goriponsoft/16bitBank-MEGAROM-Controller-74670/16bitBank-MEGAROM-Controller_74670.kicad_sch

## KiCad design 16bitBank-MEGAROM-Controller_74670.kicad_sch (2024-03-24)

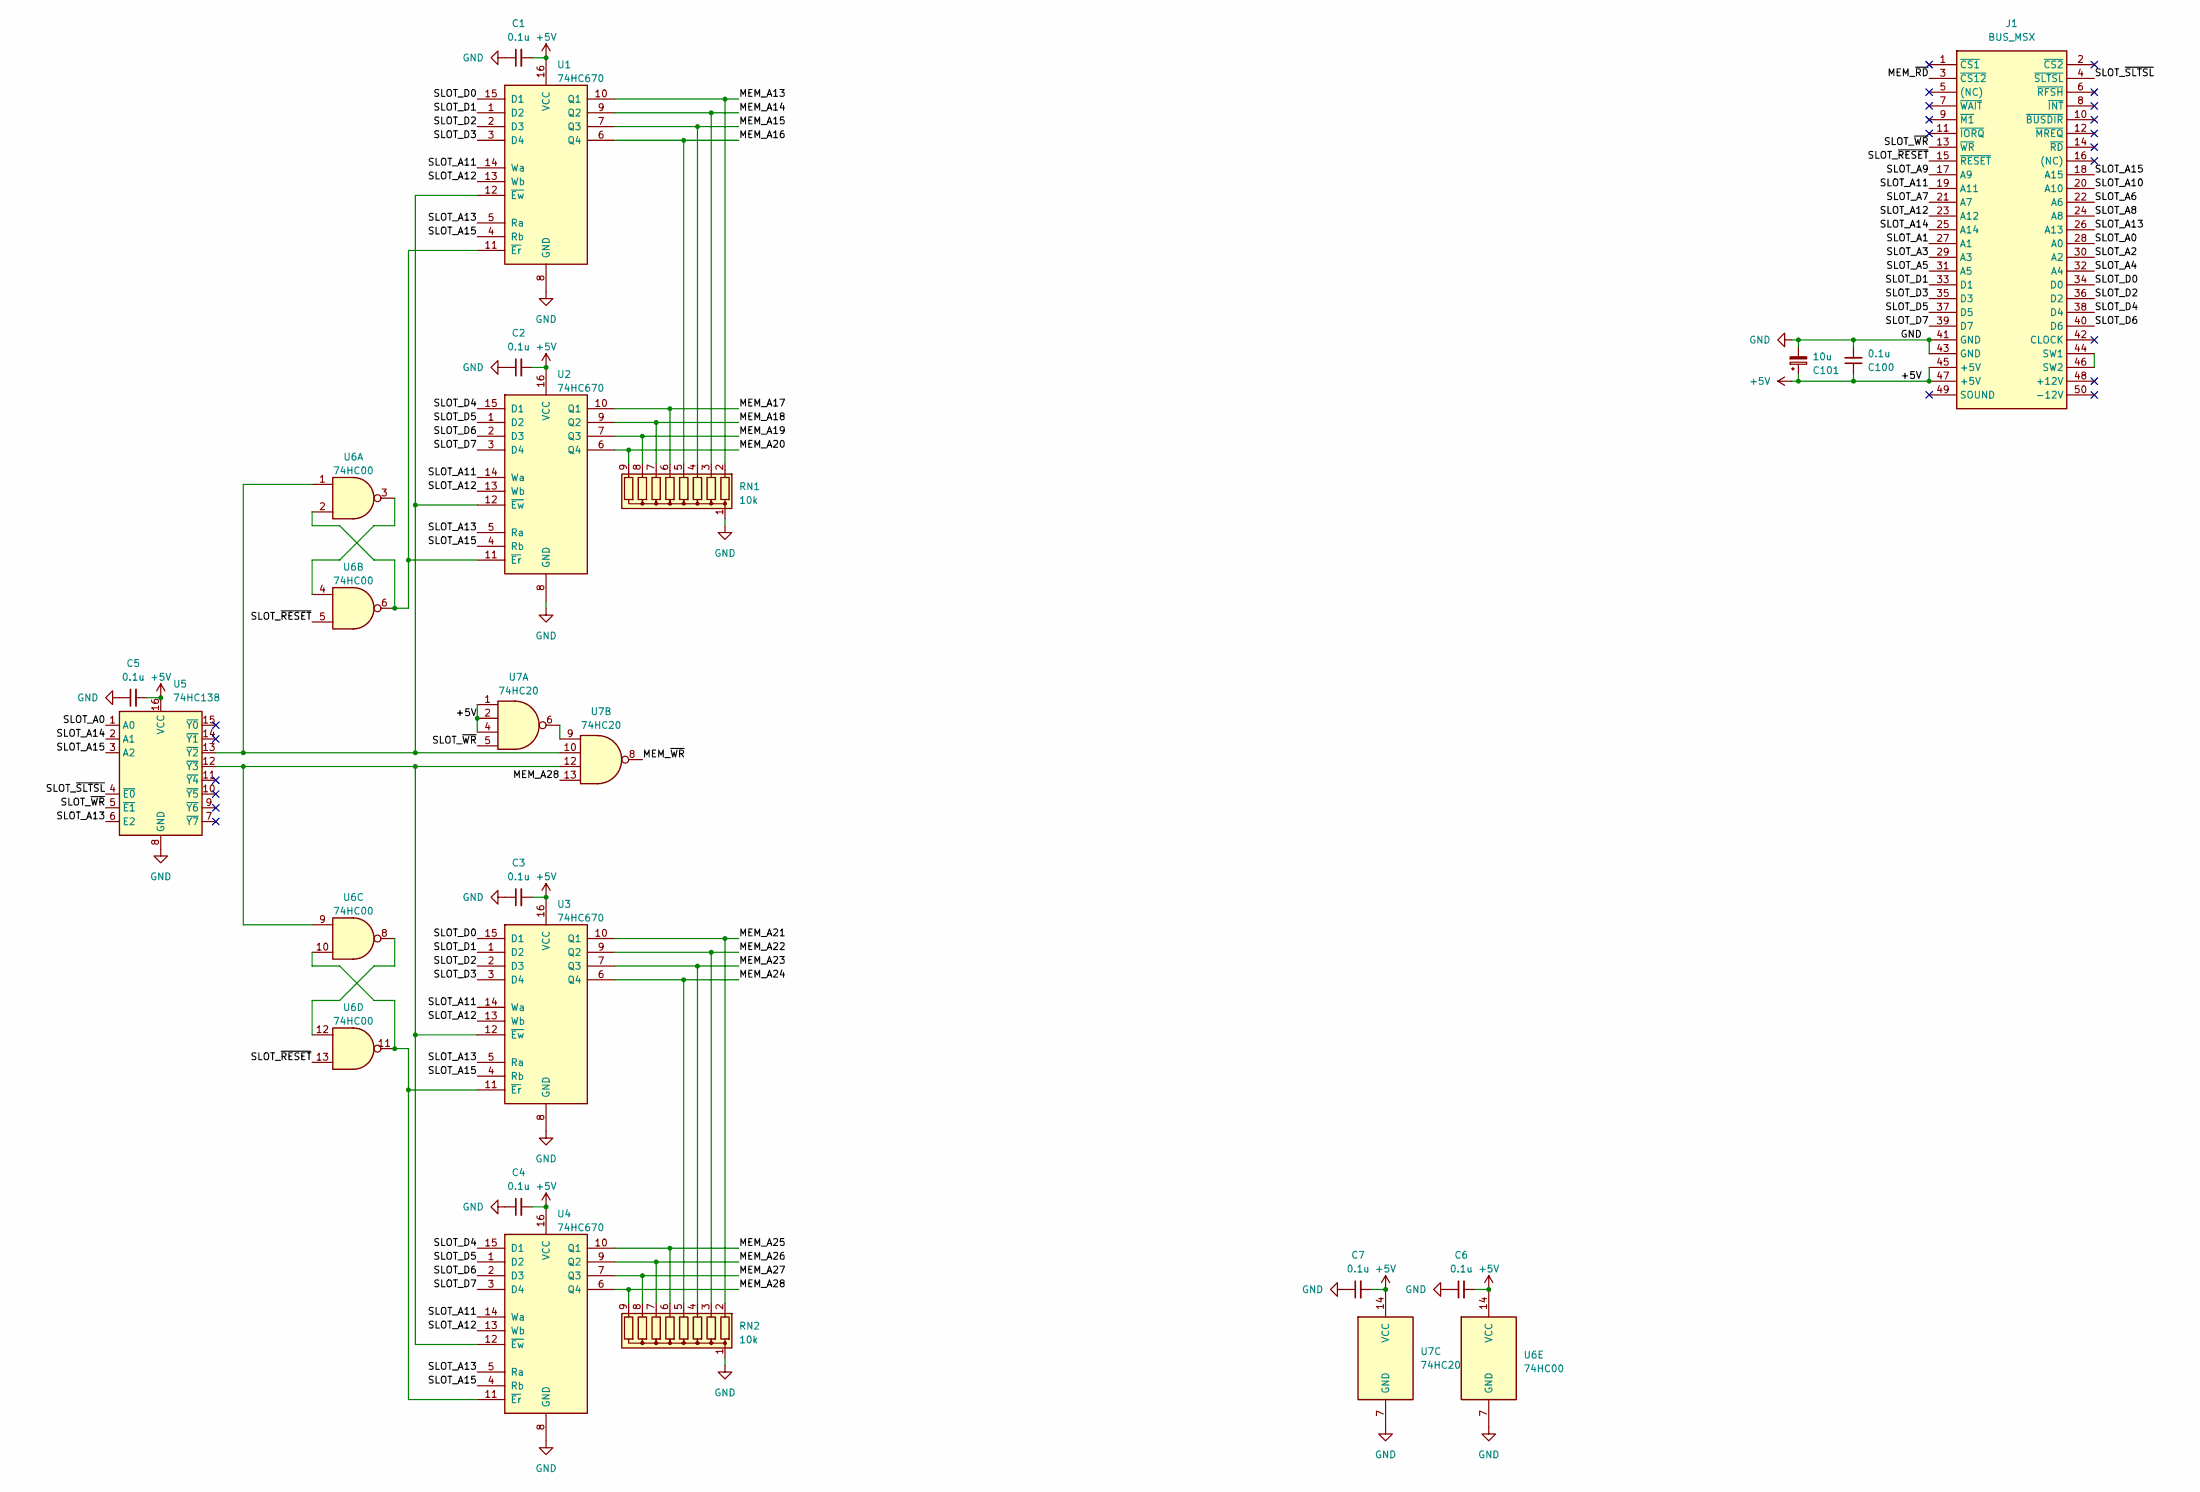
[picture p2: schematic 16bitBank-MEGAROM-Controller_74670.kicad_sch]

Parts:
C1, C2, C3, C4, C5, C6, C7, C100: 0.1u
C101: 10u
J1: BUS_MSX; BUS_MSX_SHORT_CARD
RN1, RN2: 10k
U1, U2, U3, U4: 74HC670
U5: 74HC138
U6: 74HC00
U7: 74HC20

Connections:
+5V: C1.2, C2.2, C3.2, C4.2, C5.2, C6.2, C7.2, C100.1, C101.1, J1.45 (+5V), J1.47 (+5V), U1.16 (VCC), U2.16 (VCC), U3.16 (VCC), U4.16 (VCC), U5.16 (VCC), U6.14 (VCC), U7.1, U7.2, U7.4, U7.14 (VCC)
GND: C1.1, C2.1, C3.1, C4.1, C5.1, C6.1, C7.1, C100.2, C101.2, J1.41 (GND), J1.43 (GND), RN1.1 (common), RN2.1 (common), U1.8 (GND), U2.8 (GND), U3.8 (GND), U4.8 (GND), U5.8 (GND), U6.7 (GND), U7.7 (GND)
MEM_A13: RN1.2 (R1), U1.10 (Q1)
MEM_A14: RN1.3 (R2), U1.9 (Q2)
MEM_A15: RN1.4 (R3), U1.7 (Q3)
MEM_A16: RN1.5 (R4), U1.6 (Q4)
MEM_A17: RN1.6 (R5), U2.10 (Q1)
MEM_A18: RN1.7 (R6), U2.9 (Q2)
MEM_A19: RN1.8 (R7), U2.7 (Q3)
MEM_A20: RN1.9 (R8), U2.6 (Q4)
MEM_A21: RN2.2 (R1), U3.10 (Q1)
MEM_A22: RN2.3 (R2), U3.9 (Q2)
MEM_A23: RN2.4 (R3), U3.7 (Q3)
MEM_A24: RN2.5 (R4), U3.6 (Q4)
MEM_A25: RN2.6 (R5), U4.10 (Q1)
MEM_A26: RN2.7 (R6), U4.9 (Q2)
MEM_A27: RN2.8 (R7), U4.7 (Q3)
MEM_A28: RN2.9 (R8), U4.6 (Q4), U7.13
MEM_~RD: J1.3 (~CS12)
MEM_~WR: U7.8
unnamed: J1.44 (SW1), J1.46 (SW2)
unnamed: U1.11 (~Er), U2.11 (~Er), U6.2, U6.6
unnamed: U1.12 (~Ew), U2.12 (~Ew), U5.13 (~Y2), U6.1, U7.10
unnamed: U3.11 (~Er), U4.11 (~Er), U6.10, U6.11
unnamed: U3.12 (~Ew), U4.12 (~Ew), U5.12 (~Y3), U6.9, U7.12
unnamed: U6.3, U6.4
unnamed: U6.8, U6.12
unnamed: U7.6, U7.9
SLOT_A0: J1.28 (A0), U5.1 (A0)
SLOT_A1: J1.27 (A1)
SLOT_A2: J1.30 (A2)
SLOT_A3: J1.29 (A3)
SLOT_A4: J1.32 (A4)
SLOT_A5: J1.31 (A5)
SLOT_A6: J1.22 (A6)
SLOT_A7: J1.21 (A7)
SLOT_A8: J1.24 (A8)
SLOT_A9: J1.17 (A9)
SLOT_A10: J1.20 (A10)
SLOT_A11: J1.19 (A11), U1.14 (Wa), U2.14 (Wa), U3.14 (Wa), U4.14 (Wa)
SLOT_A12: J1.23 (A12), U1.13 (Wb), U2.13 (Wb), U3.13 (Wb), U4.13 (Wb)
SLOT_A13: J1.26 (A13), U1.5 (Ra), U2.5 (Ra), U3.5 (Ra), U4.5 (Ra), U5.6 (E2)
SLOT_A14: J1.25 (A14), U5.2 (A1)
SLOT_A15: J1.18 (A15), U1.4 (Rb), U2.4 (Rb), U3.4 (Rb), U4.4 (Rb), U5.3 (A2)
SLOT_D0: J1.34 (D0), U1.15 (D1), U3.15 (D1)
SLOT_D1: J1.33 (D1), U1.1 (D2), U3.1 (D2)
SLOT_D2: J1.36 (D2), U1.2 (D3), U3.2 (D3)
SLOT_D3: J1.35 (D3), U1.3 (D4), U3.3 (D4)
SLOT_D4: J1.38 (D4), U2.15 (D1), U4.15 (D1)
SLOT_D5: J1.37 (D5), U2.1 (D2), U4.1 (D2)
SLOT_D6: J1.40 (D6), U2.2 (D3), U4.2 (D3)
SLOT_D7: J1.39 (D7), U2.3 (D4), U4.3 (D4)
SLOT_~RESET: J1.15 (~RESET), U6.5, U6.13
SLOT_~SLTSL: J1.4 (~SLTSL), U5.4 (~E0)
SLOT_~WR: J1.13 (~WR), U5.5 (~E1), U7.5
